Asyny/embeddedBridge/Software/src/CommandHandling/CommandHandler.cpp

#include "CommandHandling/CommandHandler.h"



void CommandHandler::setup() {
    // Do some generic pre-processing here
    doSetup();
    // Do some generic post-processing here
}


void CommandHandler::process() {
    // Do some generic pre-processing here
    doProcess();
    // Do some generic post-processing here
}
